dantudose/Hacktor-Watch/Images/20250808_135845.jpg

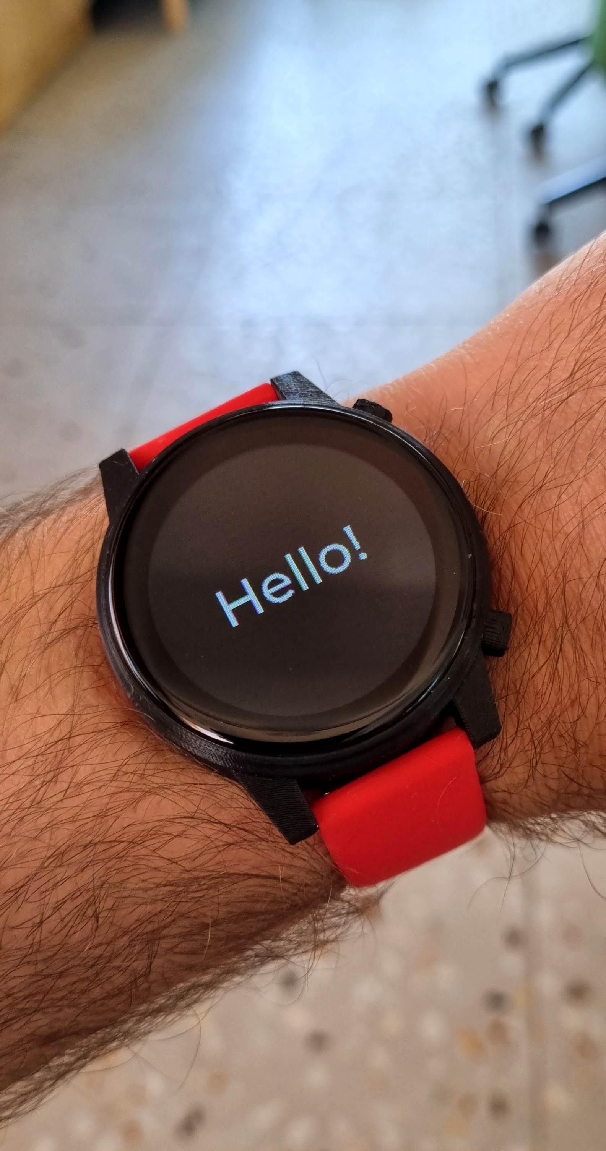
Images/20250808_135845.jpg
